YeetTheAnson/RFly-One/cartScreenshots/AliExpressCart.png

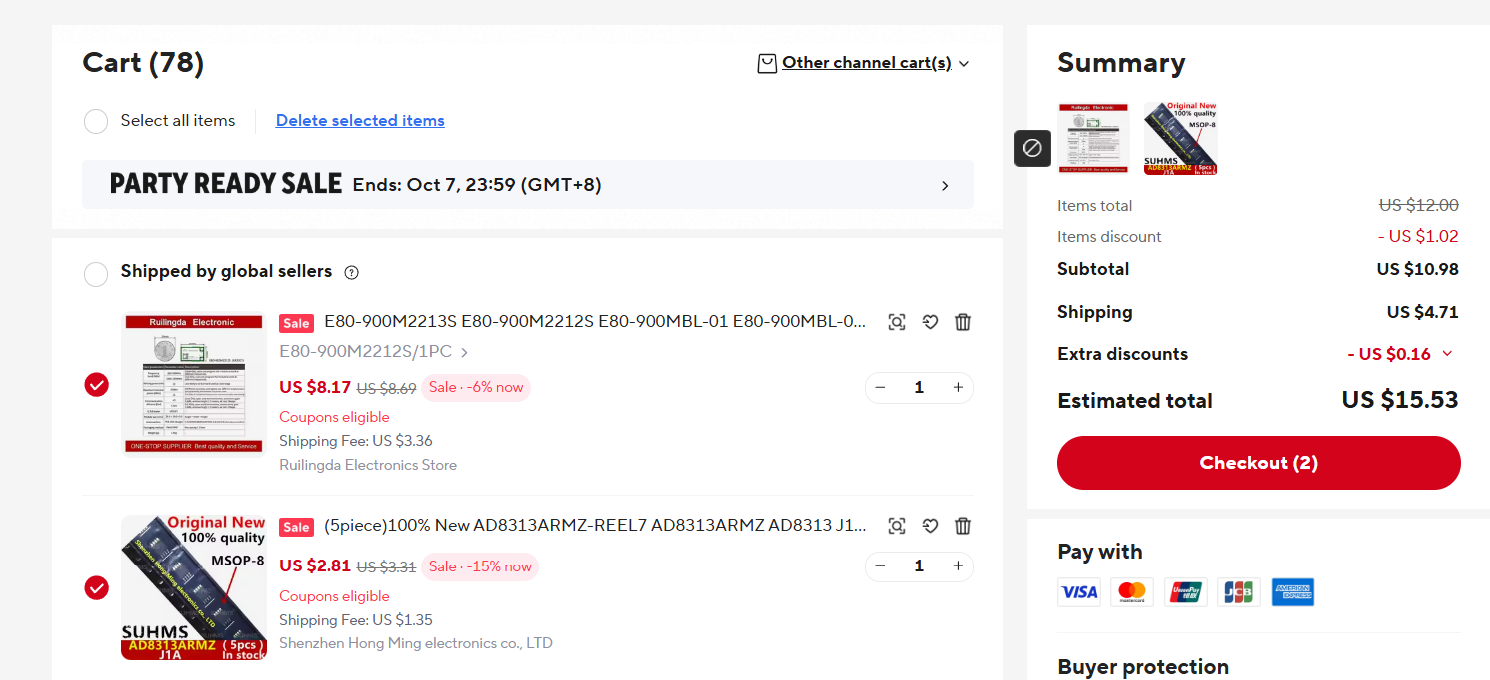
cartScreenshots/AliExpressCart.png
