YeetTheAnson/RFly-One/cartScreenshots/JLCPCBCart.png

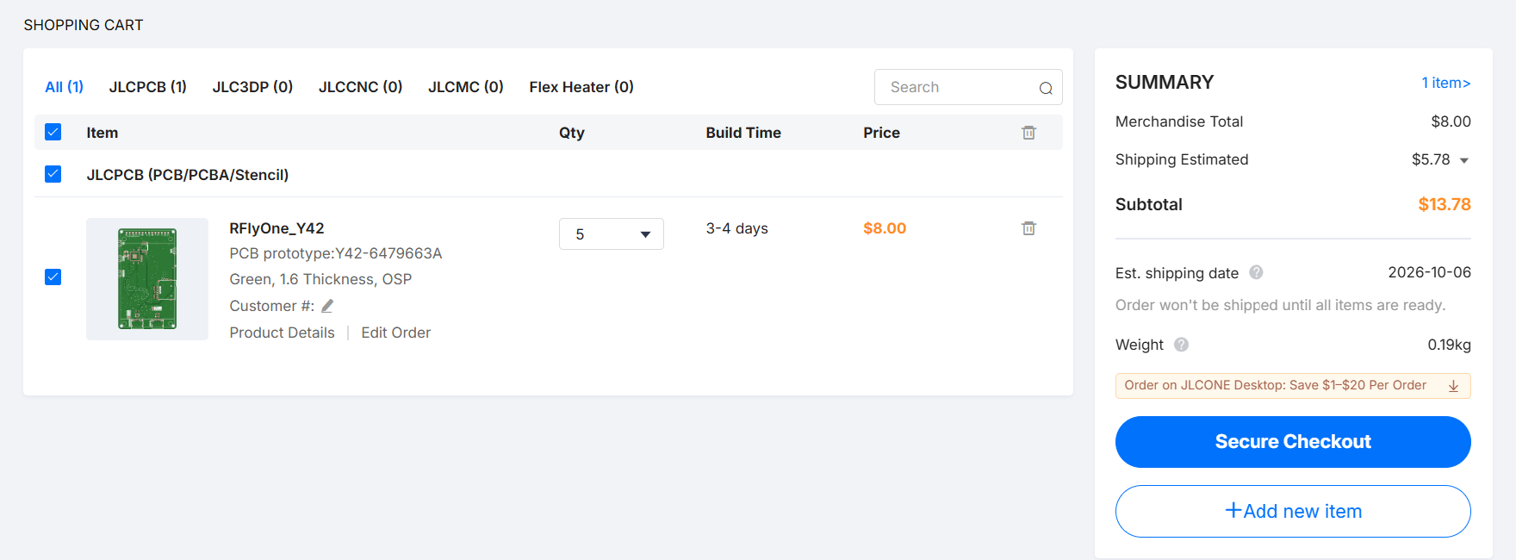
cartScreenshots/JLCPCBCart.png
