YeetTheAnson/RFly-One/cartScreenshots/JLCPCBShipping.png

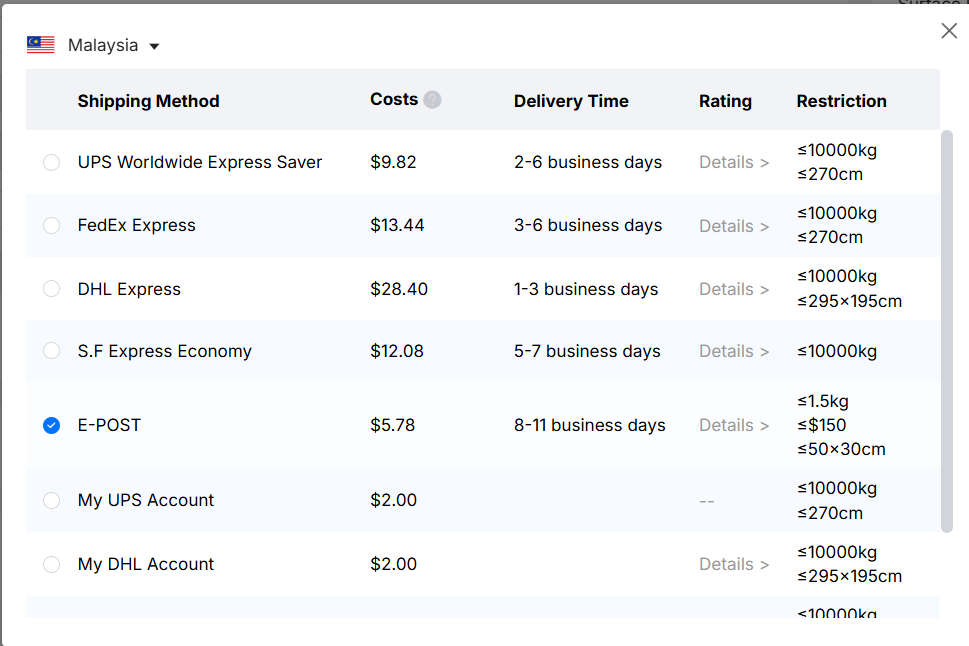
cartScreenshots/JLCPCBShipping.png
