YeetTheAnson/RFly-One/cartScreenshots/ShopeeCart.png

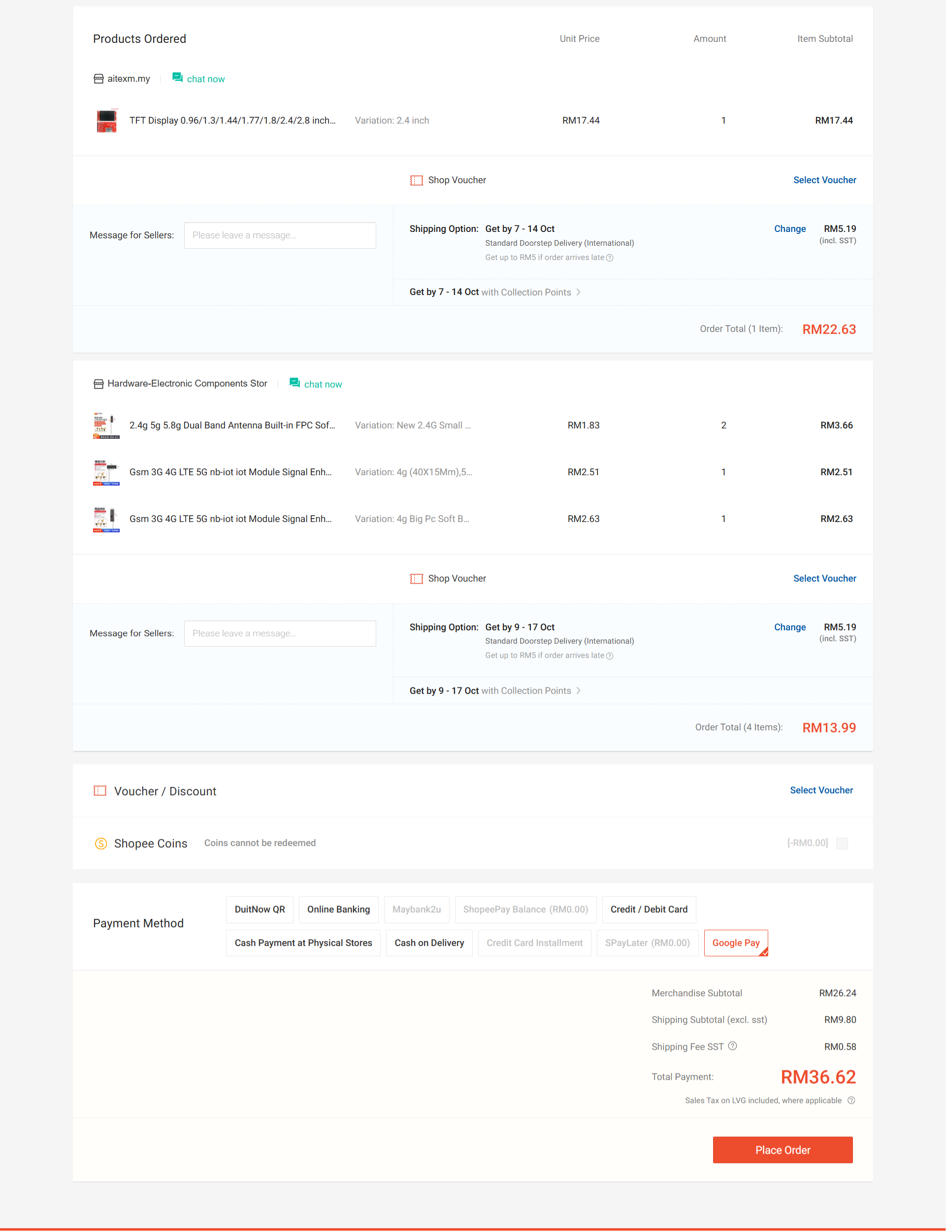
cartScreenshots/ShopeeCart.png
